DynamixYANG/highendusb3hub/pic/JPEG/2019-02-21_172800.png

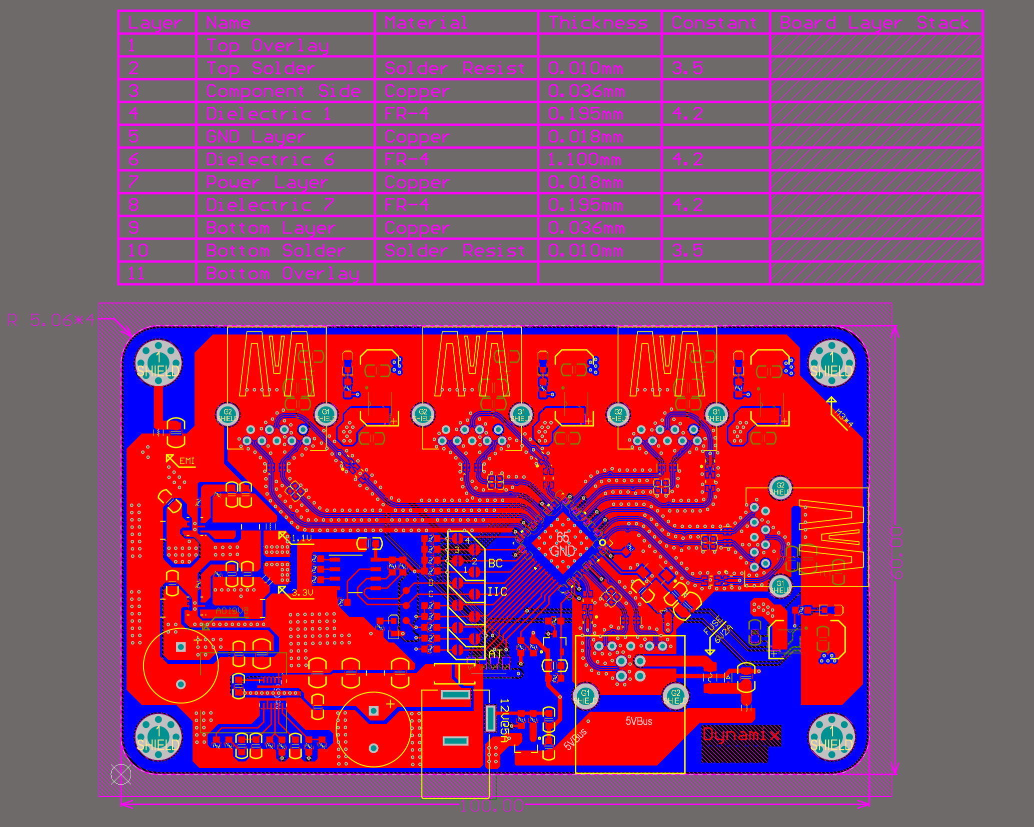
pic/JPEG/2019-02-21_172800.png
