DynamixYANG/highendusb3hub/pic/JPEG/IMG_201902211620290.jpg

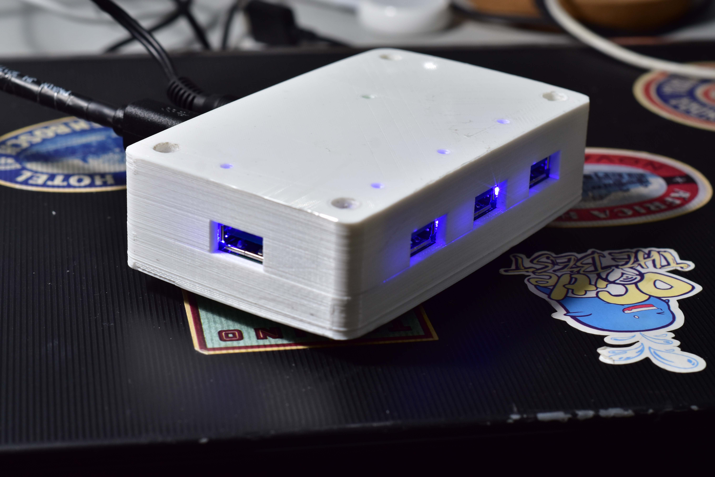
pic/JPEG/IMG_201902211620290.jpg
