DynamixYANG/highendusb3hub/pic/JPEG/IMG_201902211620291.jpg

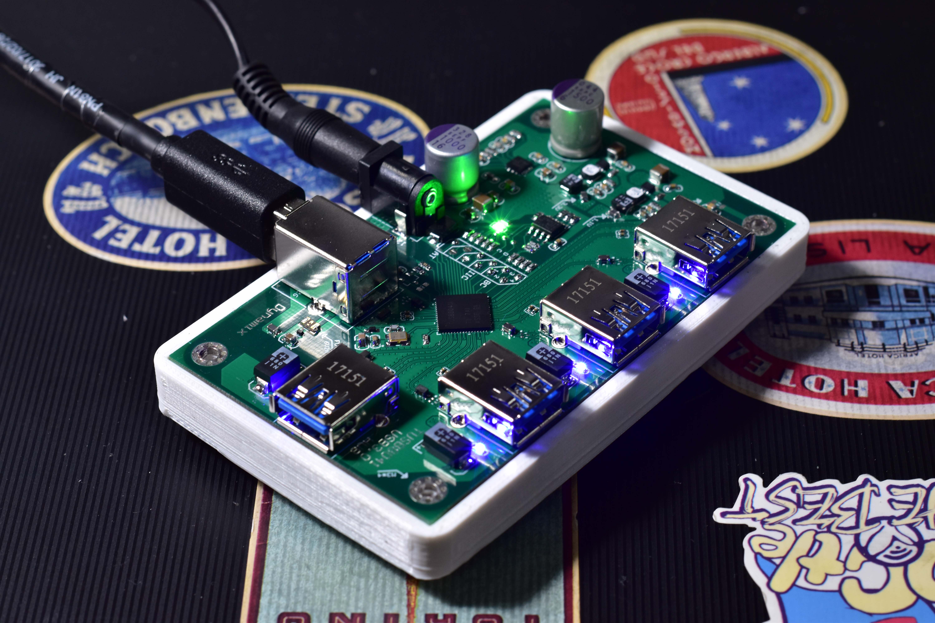
pic/JPEG/IMG_201902211620291.jpg
