DynamixYANG/highendusb3hub/pic/JPEG/IMG_201902211620294.jpg

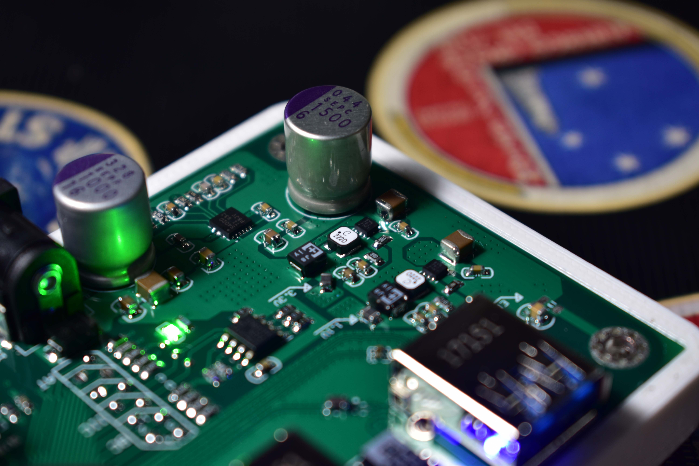
pic/JPEG/IMG_201902211620294.jpg
