DynamixYANG/highendusb3hub/pic/JPEG/IMG_201902211620295.jpg

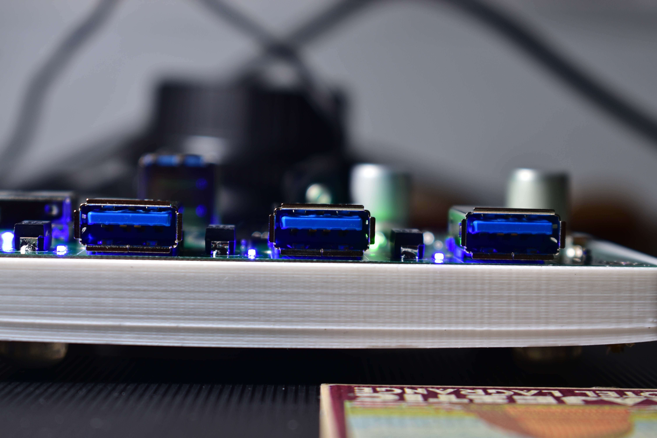
pic/JPEG/IMG_201902211620295.jpg
