DynamixYANG/highendusb3hub/pic/JPEG/IMG_201902211620296.jpg

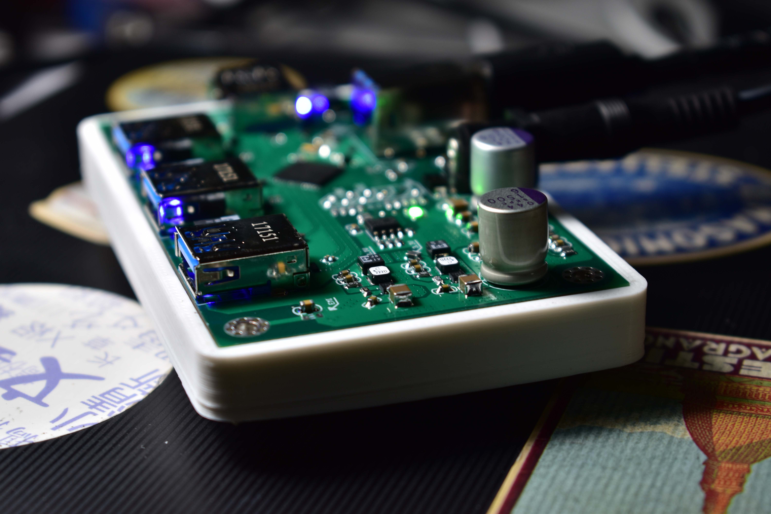
pic/JPEG/IMG_201902211620296.jpg
