DynamixYANG/highendusb3hub/pic/JPEG/IMG_201902211620297.jpg

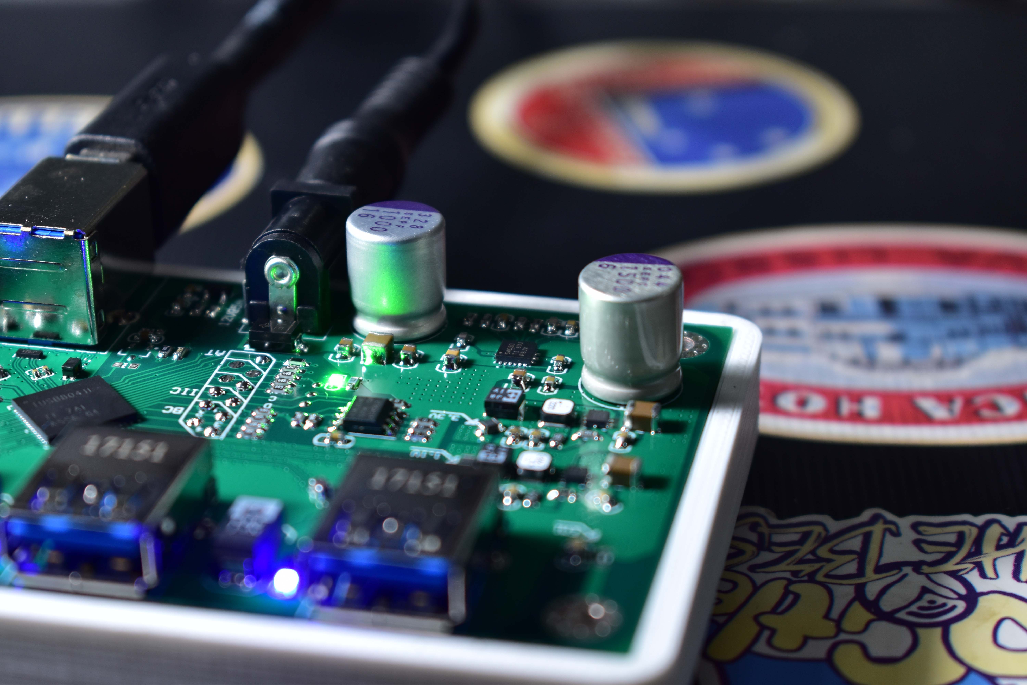
pic/JPEG/IMG_201902211620297.jpg
