DynamixYANG/highendusb3hub/pic/JPEG/IMG_201902211620298.jpg

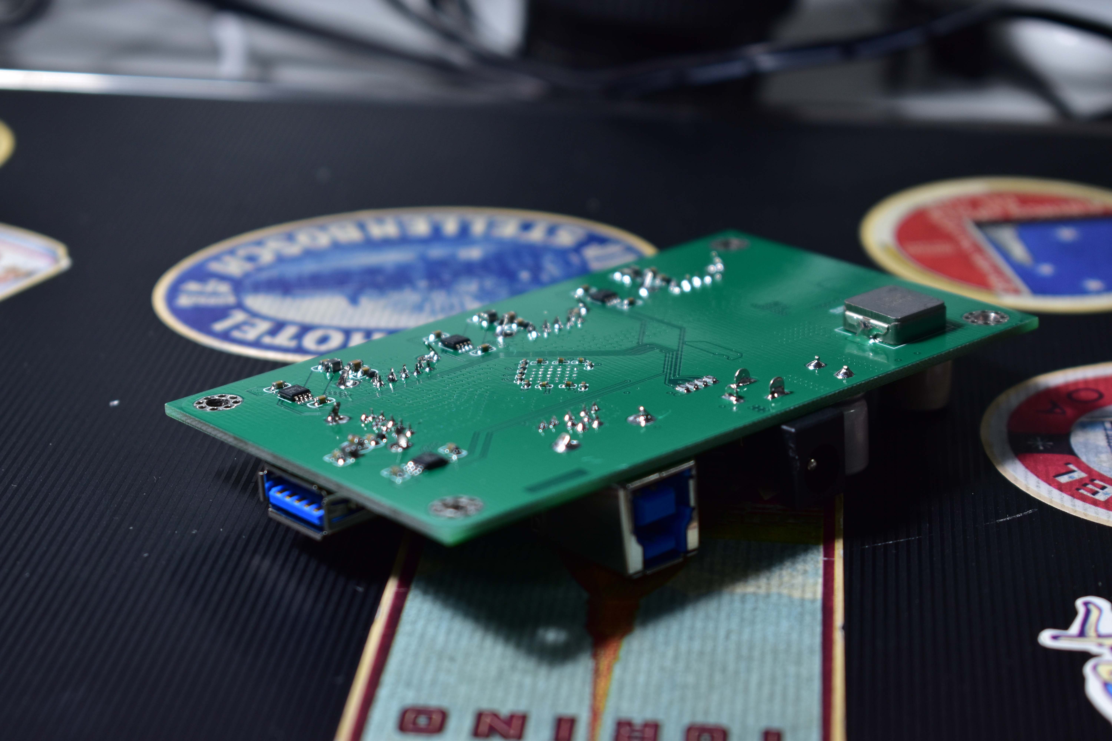
pic/JPEG/IMG_201902211620298.jpg
