DynamixYANG/highendusb3hub/pic/JPEG/IMG_201902211620299.jpg

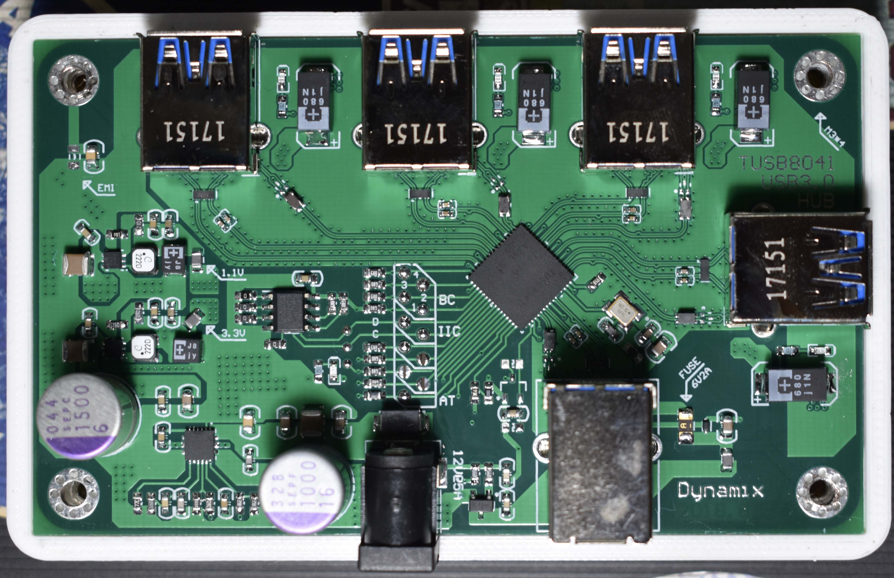
pic/JPEG/IMG_201902211620299.jpg
