DynamixYANG/highendusb3hub/pic/JPEG/IMG_2019022116202912.jpg

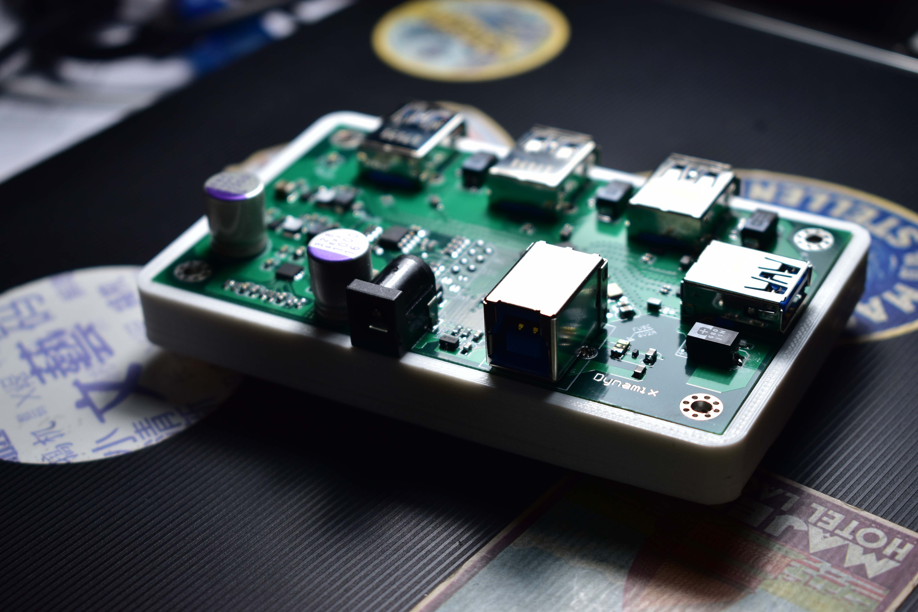
pic/JPEG/IMG_2019022116202912.jpg
